antmicro/lpddr5-testbed/assets/previews/layer2.png

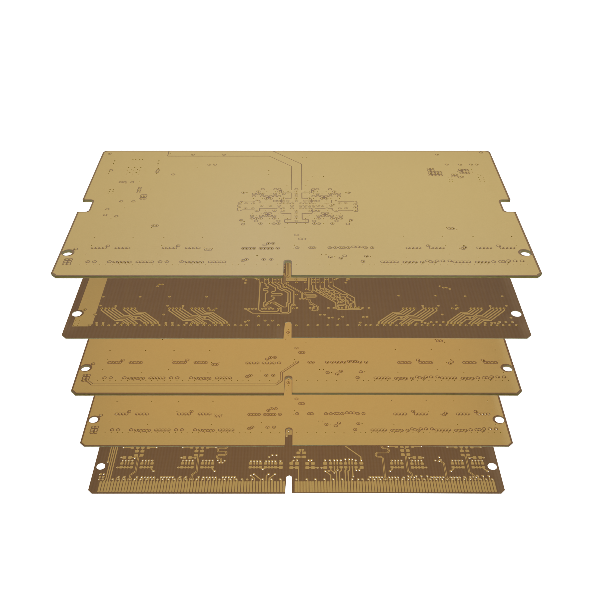
assets/previews/layer2.png
