antmicro/lpddr5-testbed/assets/previews/layer3.webp

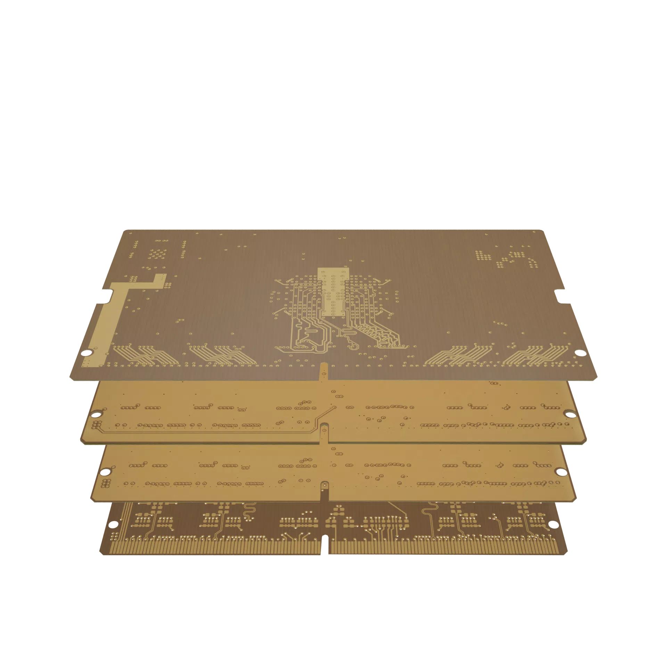
assets/previews/layer3.webp
