antmicro/lpddr5-testbed/assets/previews/layer4.png

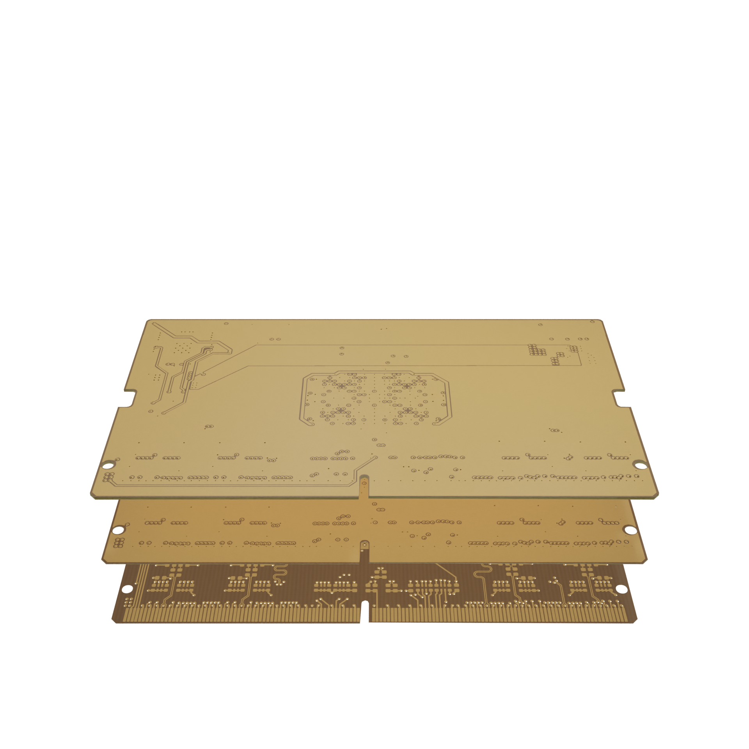
assets/previews/layer4.png
