antmicro/lpddr5-testbed/assets/previews/layer5.png

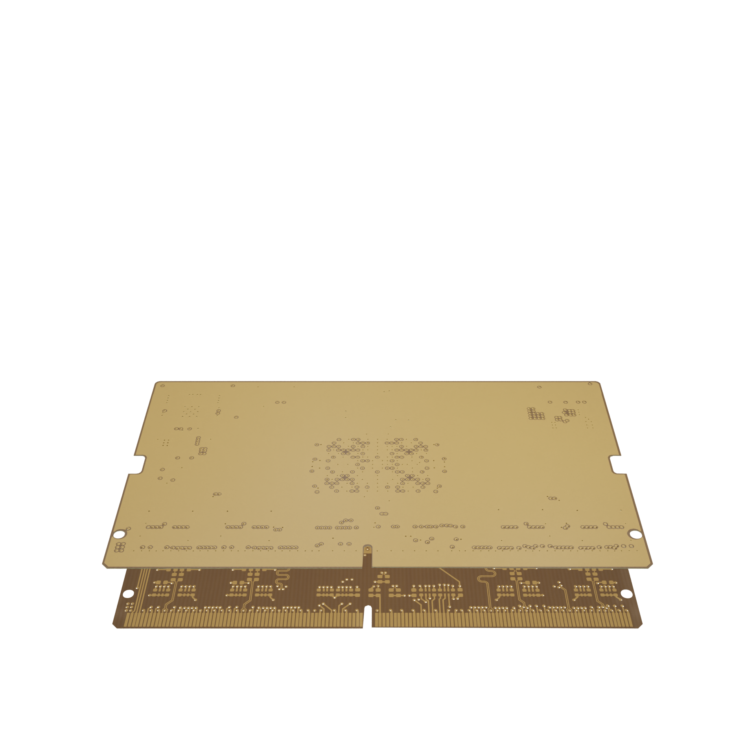
assets/previews/layer5.png
