antmicro/lpddr5-testbed/assets/previews/leftB.png

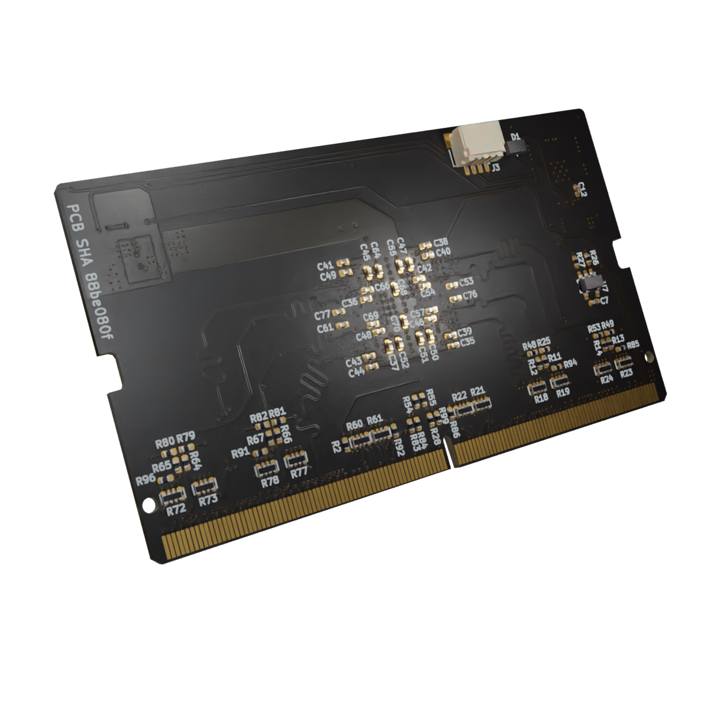
assets/previews/leftB.png
