antmicro/lpddr5-testbed/assets/previews/orthoB.png

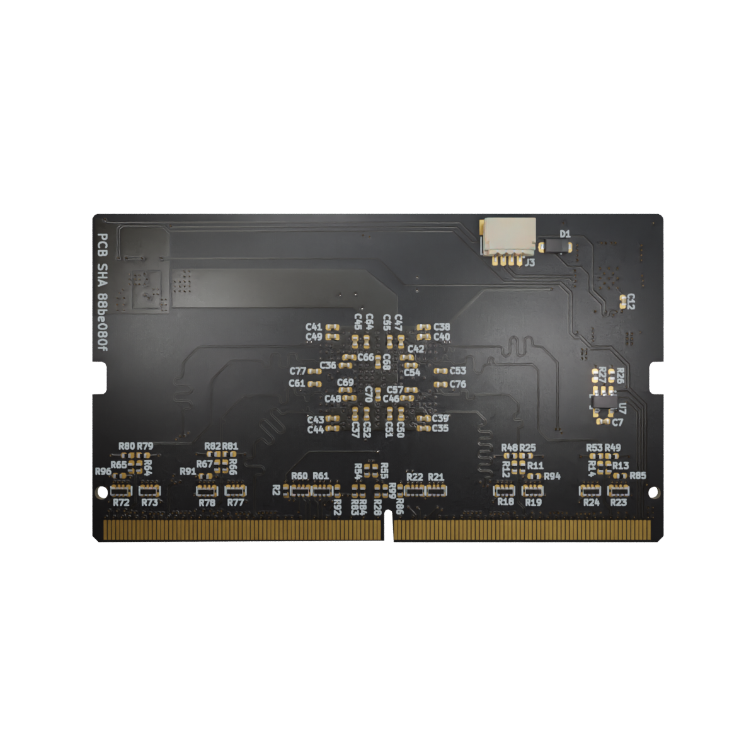
assets/previews/orthoB.png
