antmicro/lpddr5-testbed/assets/previews/orthoT.png

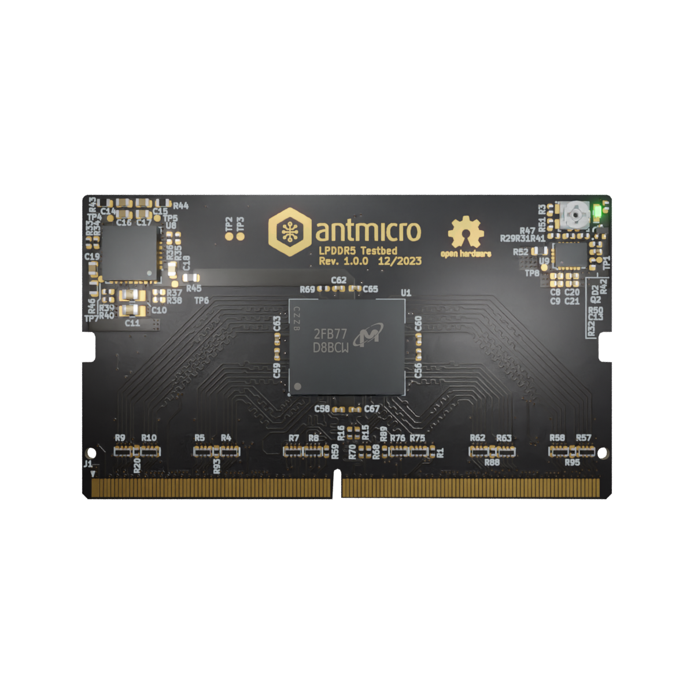
assets/previews/orthoT.png
