antmicro/lpddr5-testbed/assets/previews/photoB.png

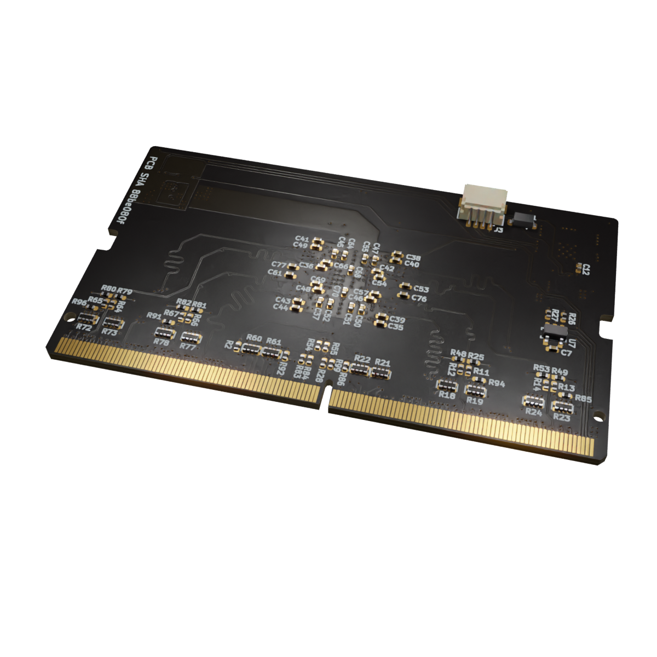
assets/previews/photoB.png
