antmicro/lpddr5-testbed/assets/previews/rightB.png

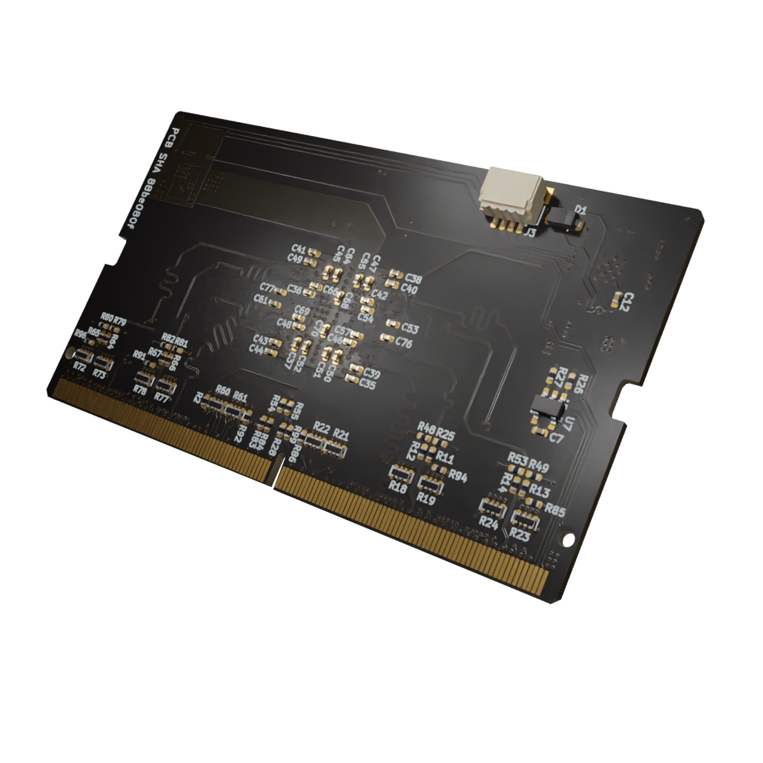
assets/previews/rightB.png
