antmicro/lpddr5-testbed/lpddr5-testbed.kicad_sch

## KiCad design lpddr5-testbed.kicad_sch (2024-01-10)

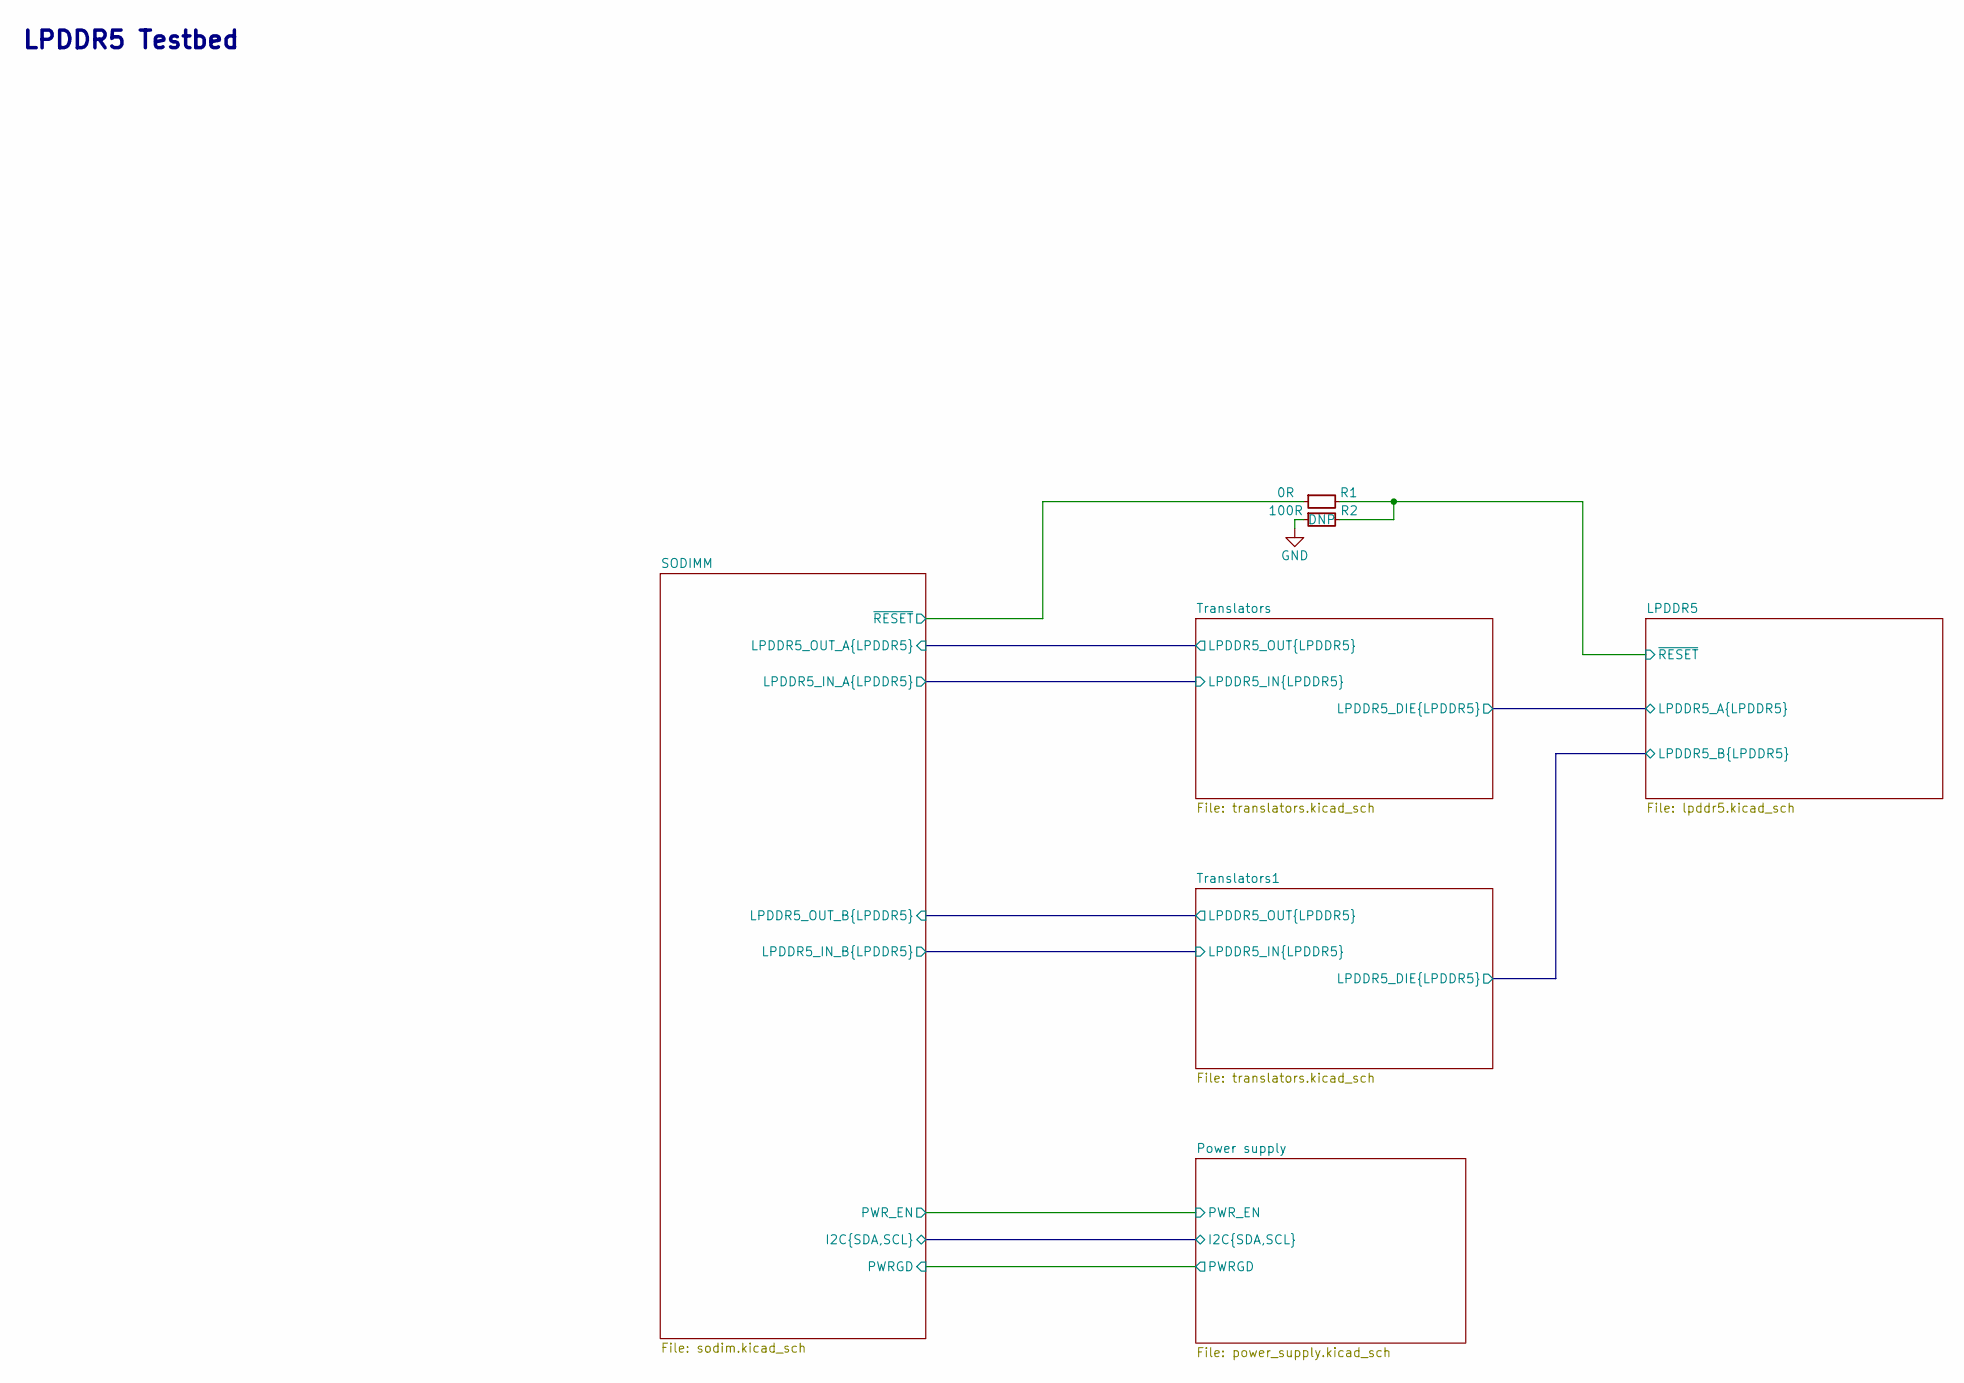
[picture p19: schematic lpddr5-testbed.kicad_sch]

Parts:
R1: R_0R_0402; R_0402_1005Metric; MPN ERJ2GE0R00X
R2: R_100R_0402; R_0402_1005Metric; Tolerance 1%; MPN CR0402-FX-1000GLF

Connections:
GND: R2.1
~RESET: R1.1, R1.2, R2.2

Notes on the sheet:
LPDDR5 Testbed
