antmicro/lpddr5-testbed/lpddr5.kicad_sch

## KiCad design lpddr5.kicad_sch (2023-12-29)

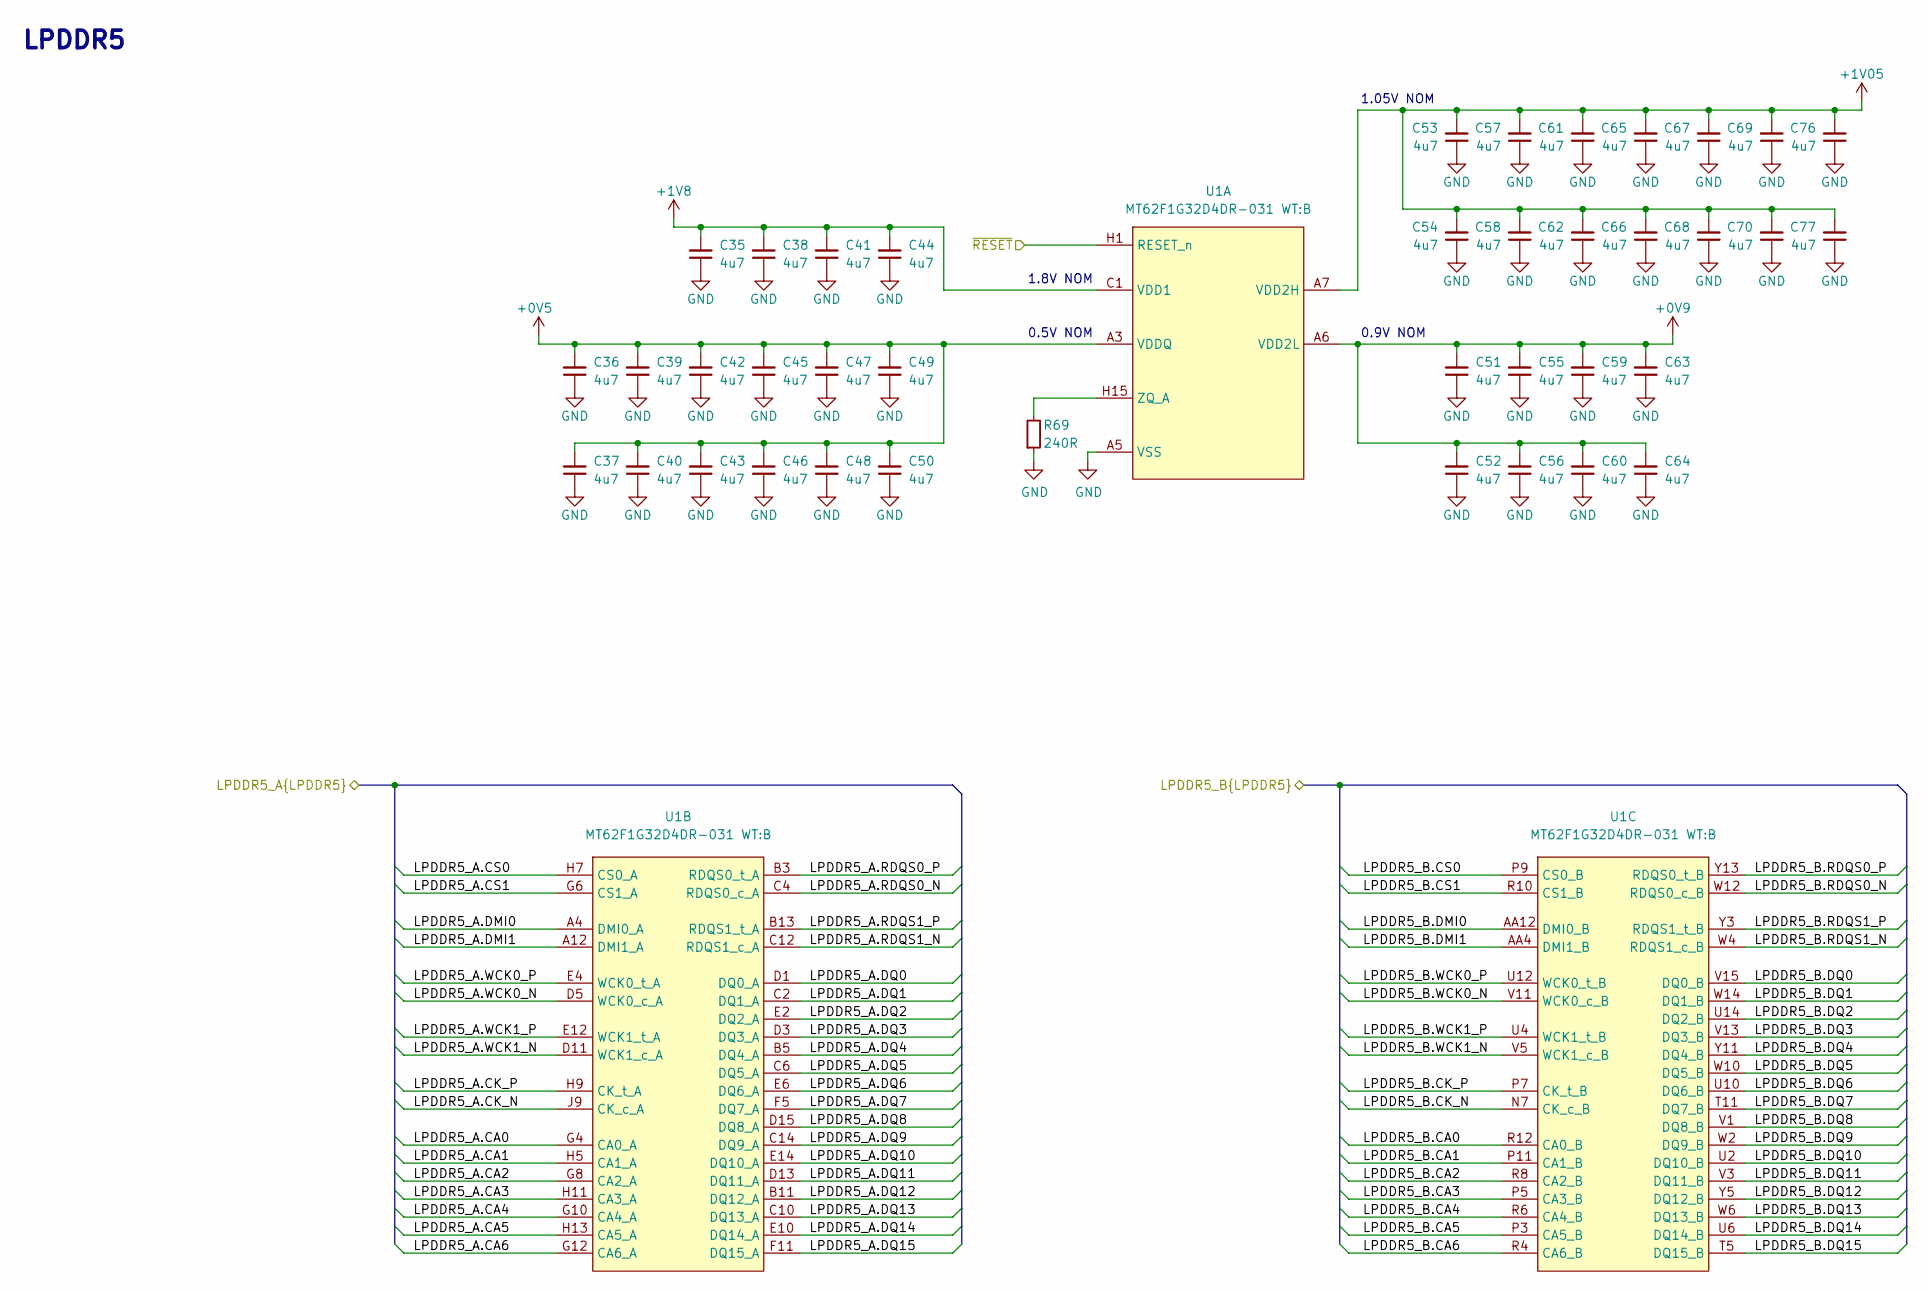
[picture p20: schematic lpddr5.kicad_sch]

Parts:
C35, C36, C37, C38, C39, C40, C41, C42, C43, C44, C45, C46, C47, C48, C49, C50, C51, C52, C53, C54, C55, C56, C57, C58, C59, C60, C61, C62, C63, C64, C65, C66, C67, C68, C69, C70, C76, C77: C_4u7_0402; C_0402_1005Metric; MPN GRM155R61A475MEAAD
R69: R_240R_0402; R_0402_1005Metric; Tolerance 1%; MPN CR0402-FX-2400GLF
U1: MT62F1G32D4DR-031; BGA-315_12.4x15mm_Layout15x21_P0.8x0.7mm; MPN MT62F1G32D4DR-031 WT:B

Connections:
+0V5: C36.2, C37.2, C39.2, C40.2, C42.2, C43.2, C45.2, C46.2, C47.2, C48.2, C49.2, C50.2, U1.A3 (VDDQ), U1.A13 (VDDQ), U1.AA3 (VDDQ), U1.AA13 (VDDQ), U1.B2 (VDDQ), U1.B14 (VDDQ), U1.C3 (VDDQ), U1.C13 (VDDQ), U1.D4 (VDDQ), U1.D12 (VDDQ), U1.E5 (VDDQ), U1.E11 (VDDQ), U1.F1 (VDDQ), U1.F3 (VDDQ), U1.F4 (VDDQ), U1.F12 (VDDQ), U1.F13 (VDDQ), U1.F15 (VDDQ), U1.G1 (VDDQ), U1.G2 (VDDQ), U1.G14 (VDDQ), U1.G15 (VDDQ), U1.R1 (VDDQ), U1.R2 (VDDQ), U1.R14 (VDDQ), U1.R15 (VDDQ), U1.T1 (VDDQ), U1.T3 (VDDQ), U1.T4 (VDDQ), U1.T12 (VDDQ), U1.T13 (VDDQ), U1.T15 (VDDQ), U1.U5 (VDDQ), U1.U11 (VDDQ), U1.V4 (VDDQ), U1.V12 (VDDQ), U1.W3 (VDDQ), U1.W13 (VDDQ), U1.Y2 (VDDQ), U1.Y14 (VDDQ)
+0V9: C51.2, C52.2, C55.2, C56.2, C59.2, C60.2, C63.2, C64.2, U1.A6 (VDD2L), U1.A10 (VDD2L), U1.AA6 (VDD2L), U1.AA10 (VDD2L), U1.B6 (VDD2L), U1.B10 (VDD2L), U1.H2 (VDD2L), U1.H14 (VDD2L), U1.J2 (VDD2L), U1.J14 (VDD2L), U1.N2 (VDD2L), U1.N14 (VDD2L), U1.P2 (VDD2L), U1.P14 (VDD2L), U1.Y6 (VDD2L), U1.Y10 (VDD2L)
+1V05: C53.2, C54.2, C57.2, C58.2, C61.2, C62.2, C65.2, C66.2, C67.2, C68.2, C69.2, C70.2, C76.2, C77.2, U1.A7 (VDD2H), U1.A8 (VDD2H), U1.A9 (VDD2H), U1.AA7 (VDD2H), U1.AA8 (VDD2H), U1.AA9 (VDD2H), U1.B7 (VDD2H), U1.B9 (VDD2H), U1.C7 (VDD2H), U1.C9 (VDD2H), U1.D8 (VDD2H), U1.E7 (VDD2H), U1.E9 (VDD2H), U1.F6 (VDD2H), U1.F7 (VDD2H), U1.F9 (VDD2H), U1.F10 (VDD2H), U1.J5 (VDD2H), U1.J11 (VDD2H), U1.K1 (VDD2H), U1.K2 (VDD2H), U1.K3 (VDD2H), U1.K4 (VDD2H), U1.K5 (VDD2H), U1.K6 (VDD2H), U1.K10 (VDD2H), U1.K11 (VDD2H), U1.K12 (VDD2H), U1.K13 (VDD2H), U1.K14 (VDD2H), U1.K15 (VDD2H), U1.L6 (VDD2H), U1.L7 (VDD2H), U1.L8 (VDD2H), U1.L9 (VDD2H), U1.L10 (VDD2H), U1.M1 (VDD2H), U1.M2 (VDD2H), U1.M3 (VDD2H), U1.M4 (VDD2H), U1.M5 (VDD2H), U1.M6 (VDD2H), U1.M10 (VDD2H), U1.M11 (VDD2H), U1.M12 (VDD2H), U1.M13 (VDD2H), U1.M14 (VDD2H), U1.M15 (VDD2H), U1.N5 (VDD2H), U1.N11 (VDD2H), U1.T6 (VDD2H), U1.T7 (VDD2H), U1.T9 (VDD2H), U1.T10 (VDD2H), U1.U7 (VDD2H), U1.U9 (VDD2H), U1.V8 (VDD2H), U1.W7 (VDD2H), U1.W9 (VDD2H), U1.Y7 (VDD2H), U1.Y9 (VDD2H)
+1V8: C35.2, C38.2, C41.2, C44.2, U1.C1 (VDD1), U1.C15 (VDD1), U1.W1 (VDD1), U1.W15 (VDD1)
GND: C35.1, C36.1, C37.1, C38.1, C39.1, C40.1, C41.1, C42.1, C43.1, C44.1, C45.1, C46.1, C47.1, C48.1, C49.1, C50.1, C51.1, C52.1, C53.1, C54.1, C55.1, C56.1, C57.1, C58.1, C59.1, C60.1, C61.1, C62.1, C63.1, C64.1, C65.1, C66.1, C67.1, C68.1, C69.1, C70.1, C76.1, C77.1, R69.1, U1.A5 (VSS), U1.A11 (VSS), U1.AA5 (VSS), U1.AA11 (VSS), U1.B4 (VSS), U1.B8 (VSS), U1.B12 (VSS), U1.C5 (VSS), U1.C8 (VSS), U1.C11 (VSS), U1.D2 (VSS), U1.D6 (VSS), U1.D7 (VSS), U1.D9 (VSS), U1.D10 (VSS), U1.D14 (VSS), U1.E1 (VSS), U1.E3 (VSS), U1.E8 (VSS), U1.E13 (VSS), U1.E15 (VSS), U1.F2 (VSS), U1.F8 (VSS), U1.F14 (VSS), U1.G3 (VSS), U1.G5 (VSS), U1.G7 (VSS), U1.G9 (VSS), U1.G11 (VSS), U1.G13 (VSS), U1.H3 (VSS), U1.H4 (VSS), U1.H6 (VSS), U1.H8 (VSS), U1.H10 (VSS), U1.H12 (VSS), U1.J1 (VSS), U1.J3 (VSS), U1.J7 (VSS), U1.J8 (VSS), U1.J10 (VSS), U1.J12 (VSS), U1.J13 (VSS), U1.J15 (VSS), U1.K7 (VSS), U1.K8 (VSS), U1.K9 (VSS), U1.L1 (VSS), U1.L2 (VSS), U1.L3 (VSS), U1.L4 (VSS), U1.L5 (VSS), U1.L11 (VSS), U1.L12 (VSS), U1.L13 (VSS), U1.L14 (VSS), U1.L15 (VSS), U1.M7 (VSS), U1.M8 (VSS), U1.M9 (VSS), U1.N1 (VSS), U1.N3 (VSS), U1.N4 (VSS), U1.N6 (VSS), U1.N8 (VSS), U1.N9 (VSS), U1.N10 (VSS), U1.N12 (VSS), U1.N13 (VSS), U1.N15 (VSS), U1.P4 (VSS), U1.P6 (VSS), U1.P8 (VSS), U1.P10 (VSS), U1.P12 (VSS), U1.P13 (VSS), U1.R3 (VSS), U1.R5 (VSS), U1.R7 (VSS), U1.R9 (VSS), U1.R11 (VSS), U1.R13 (VSS), U1.T2 (VSS), U1.T8 (VSS), U1.T14 (VSS), U1.U1 (VSS), U1.U3 (VSS), U1.U8 (VSS), U1.U13 (VSS), U1.U15 (VSS), U1.V2 (VSS), U1.V6 (VSS), U1.V7 (VSS), U1.V9 (VSS), U1.V10 (VSS), U1.V14 (VSS), U1.W5 (VSS), U1.W8 (VSS), U1.W11 (VSS), U1.Y4 (VSS), U1.Y8 (VSS), U1.Y12 (VSS)
LPDDR5_A.CA0: U1.G4 (CA0_A)
LPDDR5_A.CA1: U1.H5 (CA1_A)
LPDDR5_A.CA2: U1.G8 (CA2_A)
LPDDR5_A.CA3: U1.H11 (CA3_A)
LPDDR5_A.CA4: U1.G10 (CA4_A)
LPDDR5_A.CA5: U1.H13 (CA5_A)
LPDDR5_A.CA6: U1.G12 (CA6_A)
LPDDR5_A.CK_N: U1.J9 (CK_c_A)
LPDDR5_A.CK_P: U1.H9 (CK_t_A)
LPDDR5_A.CS0: U1.H7 (CS0_A)
LPDDR5_A.CS1: U1.G6 (CS1_A)
LPDDR5_A.DMI0: U1.A4 (DMI0_A)
LPDDR5_A.DMI1: U1.A12 (DMI1_A)
LPDDR5_A.DQ0: U1.D1 (DQ0_A)
LPDDR5_A.DQ1: U1.C2 (DQ1_A)
LPDDR5_A.DQ2: U1.E2 (DQ2_A)
LPDDR5_A.DQ3: U1.D3 (DQ3_A)
LPDDR5_A.DQ4: U1.B5 (DQ4_A)
LPDDR5_A.DQ5: U1.C6 (DQ5_A)
LPDDR5_A.DQ6: U1.E6 (DQ6_A)
LPDDR5_A.DQ7: U1.F5 (DQ7_A)
LPDDR5_A.DQ8: U1.D15 (DQ8_A)
LPDDR5_A.DQ9: U1.C14 (DQ9_A)
LPDDR5_A.DQ10: U1.E14 (DQ10_A)
LPDDR5_A.DQ11: U1.D13 (DQ11_A)
LPDDR5_A.DQ12: U1.B11 (DQ12_A)
LPDDR5_A.DQ13: U1.C10 (DQ13_A)
LPDDR5_A.DQ14: U1.E10 (DQ14_A)
LPDDR5_A.DQ15: U1.F11 (DQ15_A)
LPDDR5_A.RDQS0_N: U1.C4 (RDQS0_c_A)
LPDDR5_A.RDQS0_P: U1.B3 (RDQS0_t_A)
LPDDR5_A.RDQS1_N: U1.C12 (RDQS1_c_A)
LPDDR5_A.RDQS1_P: U1.B13 (RDQS1_t_A)
LPDDR5_A.WCK0_N: U1.D5 (WCK0_c_A)
LPDDR5_A.WCK0_P: U1.E4 (WCK0_t_A)
LPDDR5_A.WCK1_N: U1.D11 (WCK1_c_A)
LPDDR5_A.WCK1_P: U1.E12 (WCK1_t_A)
LPDDR5_B.CA0: U1.R12 (CA0_B)
LPDDR5_B.CA1: U1.P11 (CA1_B)
LPDDR5_B.CA2: U1.R8 (CA2_B)
LPDDR5_B.CA3: U1.P5 (CA3_B)
LPDDR5_B.CA4: U1.R6 (CA4_B)
LPDDR5_B.CA5: U1.P3 (CA5_B)
LPDDR5_B.CA6: U1.R4 (CA6_B)
LPDDR5_B.CK_N: U1.N7 (CK_c_B)
LPDDR5_B.CK_P: U1.P7 (CK_t_B)
LPDDR5_B.CS0: U1.P9 (CS0_B)
LPDDR5_B.CS1: U1.R10 (CS1_B)
LPDDR5_B.DMI0: U1.AA12 (DMI0_B)
LPDDR5_B.DMI1: U1.AA4 (DMI1_B)
LPDDR5_B.DQ0: U1.V15 (DQ0_B)
LPDDR5_B.DQ1: U1.W14 (DQ1_B)
LPDDR5_B.DQ2: U1.U14 (DQ2_B)
LPDDR5_B.DQ3: U1.V13 (DQ3_B)
LPDDR5_B.DQ4: U1.Y11 (DQ4_B)
LPDDR5_B.DQ5: U1.W10 (DQ5_B)
LPDDR5_B.DQ6: U1.U10 (DQ6_B)
LPDDR5_B.DQ7: U1.T11 (DQ7_B)
LPDDR5_B.DQ8: U1.V1 (DQ8_B)
LPDDR5_B.DQ9: U1.W2 (DQ9_B)
LPDDR5_B.DQ10: U1.U2 (DQ10_B)
LPDDR5_B.DQ11: U1.V3 (DQ11_B)
LPDDR5_B.DQ12: U1.Y5 (DQ12_B)
LPDDR5_B.DQ13: U1.W6 (DQ13_B)
LPDDR5_B.DQ14: U1.U6 (DQ14_B)
LPDDR5_B.DQ15: U1.T5 (DQ15_B)
LPDDR5_B.RDQS0_N: U1.W12 (RDQS0_c_B)
LPDDR5_B.RDQS0_P: U1.Y13 (RDQS0_t_B)
LPDDR5_B.RDQS1_N: U1.W4 (RDQS1_c_B)
LPDDR5_B.RDQS1_P: U1.Y3 (RDQS1_t_B)
LPDDR5_B.WCK0_N: U1.V11 (WCK0_c_B)
LPDDR5_B.WCK0_P: U1.U12 (WCK0_t_B)
LPDDR5_B.WCK1_N: U1.V5 (WCK1_c_B)
LPDDR5_B.WCK1_P: U1.U4 (WCK1_t_B)
unnamed: R69.2, U1.H15 (ZQ_A)
~RESET: U1.H1 (RESET_n)

Notes on the sheet:
0.5V NOM
0.9V NOM
1.05V NOM
LPDDR5
1.8V NOM
