antmicro/lpddr5-testbed/power_supply.kicad_sch

## KiCad design power_supply.kicad_sch (2024-01-03)

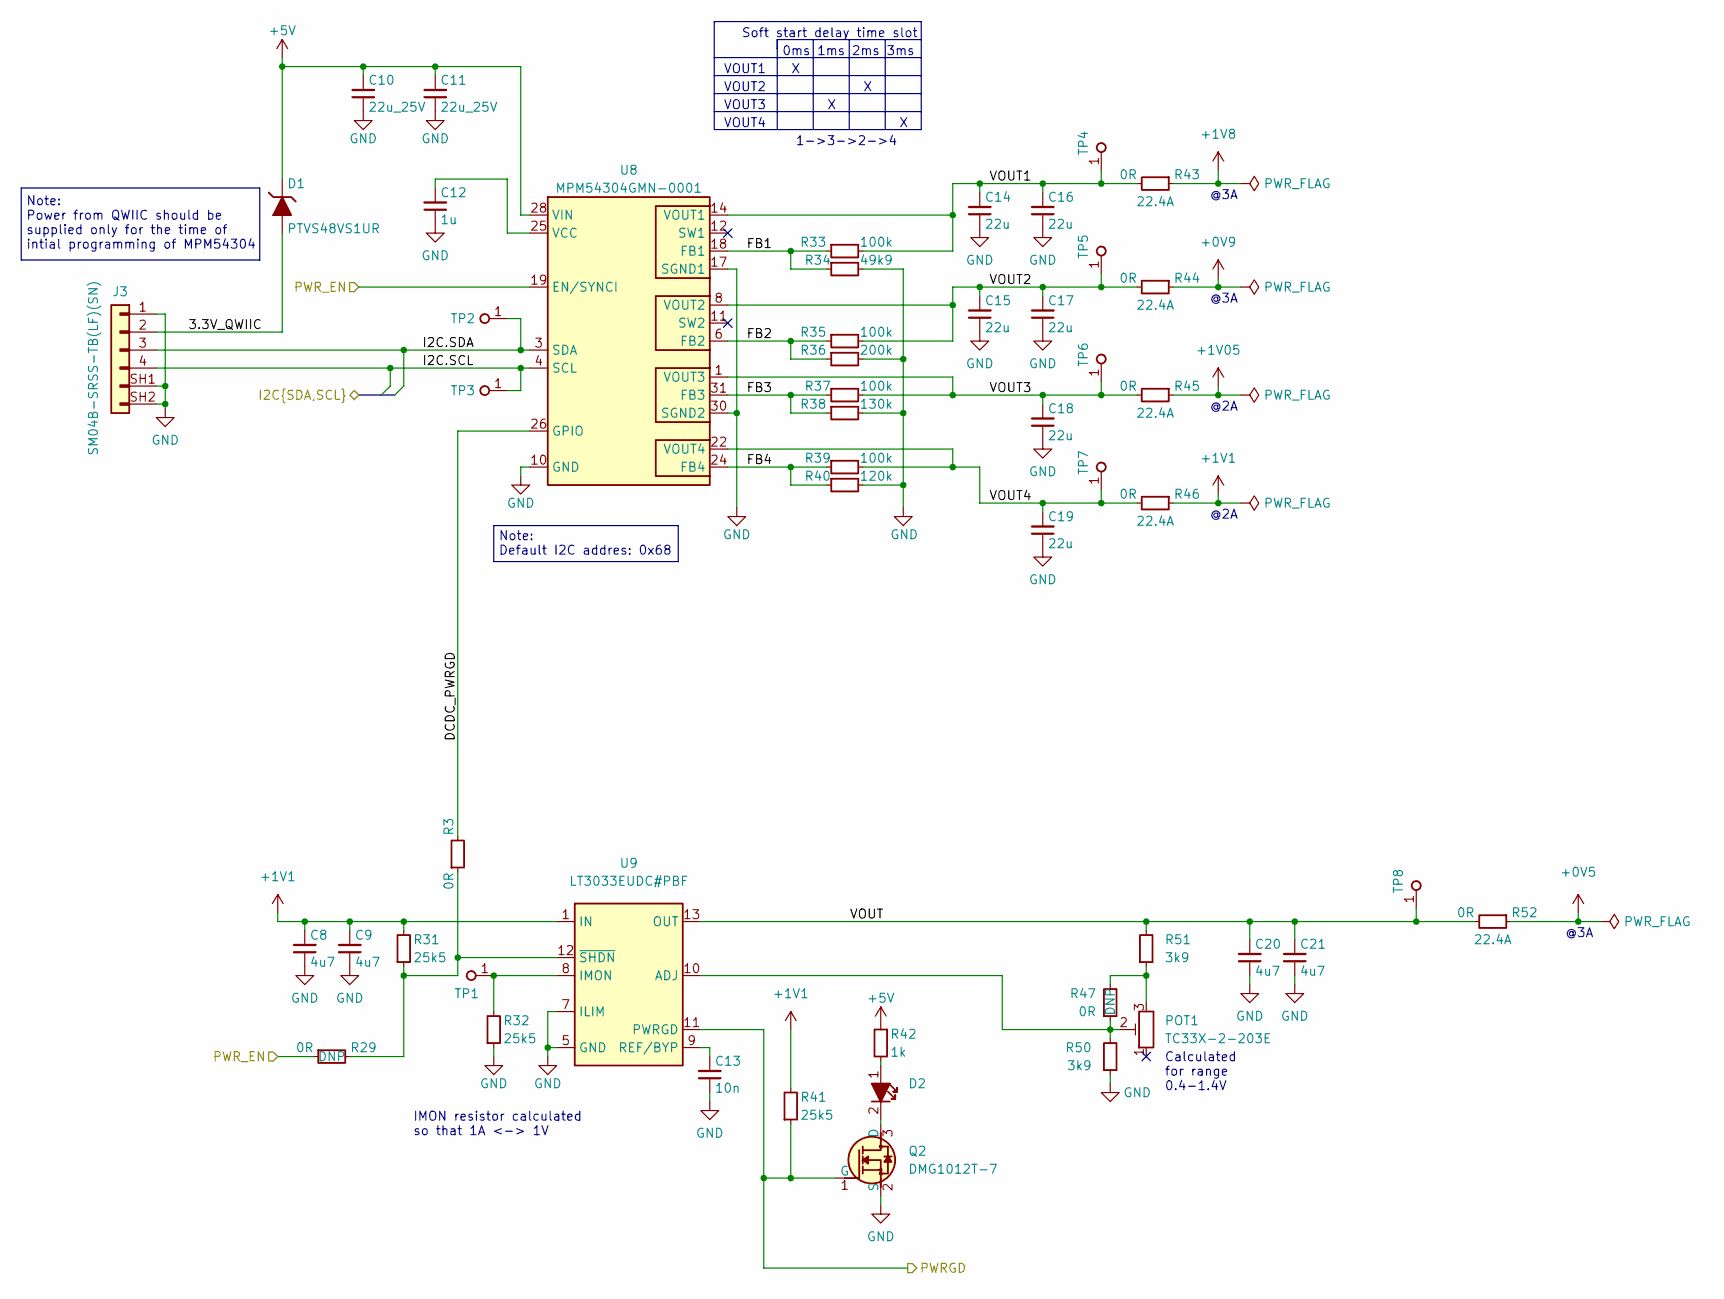
[picture p21: schematic power_supply.kicad_sch]

Parts:
C8, C9, C20, C21: C_4u7_0402; C_0402_1005Metric; MPN GRM155R61A475MEAAD
C10, C11: C_22u_25V_0805; C_0805_2012Metric; MPN CL21A226MAYNNNE
C12: C_1u_0402; C_0402_1005Metric; MPN C1005X6S1A105K050BC
C13: C_10n_0402; C_0402_1005Metric; Voltage 50V; MPN GRM155R71H103KA88D
C14, C15, C16, C17, C18, C19: C_22u_0603; C_0603_1608Metric; MPN GRM188R60J226MEA0D
D1: PTVS48VS1UR; D_SOD-123F; MPN PTVS48VS1UR,115
D2: LED_G_0603_KP-1608CGCK; LED_0603_1608Metric_G; MPN KP-1608CGCK
J3: JST_SH_1x4_SM04B-SRSS-TB-LF-SN; Conn_JST_SH_1x4_SM04B-SRSS-TB-LF-SN; MPN SM04B-SRSS-TB(LF)(SN)
POT1: TC33X-2-203E; Trimpot_3.8mmx3.6mm_TC33X-2-103E; MPN TC33X-2-203E
Q2: DMG1012T-7; SOT-523; MPN DMG1012T-7
R3, R29, R47: R_0R_0402; R_0402_1005Metric; MPN ERJ2GE0R00X
R31, R32, R41: R_25k5_0402; R_0402_1005Metric; Tolerance 1%; MPN CR0402-FX-2552GLF
R33, R35, R37, R39: R_100k_0402; R_0402_1005Metric; Tolerance 1%; MPN CR0402-FX-1003GLF
R34: R_49k9_0402; R_0402_1005Metric; Tolerance 1%; MPN CR0402-FX-4992GLF
R36: R_200k_0402; R_0402_1005Metric; Tolerance 1%; MPN CR0402-FX-2003GLF
R38: R_130k_0402; R_0402_1005Metric; Tolerance 1%; MPN CR0402-FX-1303GLF
R40: R_120k_0402; R_0402_1005Metric; Tolerance 1%; MPN CR0402-FX-1203GLF
R42: R_1k_0402; R_0402_1005Metric; Tolerance 1%; MPN CR0402-FX-1001GLF
R43, R44, R45, R46, R52: R_0R_22.4A_0603; R_0603_1608Metric; Tolerance template_tolerance; MPN PMR03EZPJ000
R50, R51: R_3k9_0402; R_0402_1005Metric; Tolerance 1%; MPN CR0402-FX-3901GLF
TP1, TP4, TP5, TP6, TP7, TP8: TP_0.75mm_SMD; TP_SMD_0.75mm
TP2, TP3: TP_1mm_SMD; TP_SMD_1mm
U8: MPM54304GMN-0001; LGA-33_7x7mm_P0.65mm; MPN MPM54304GMN-0001
U9: LT3033EUDC_QFN; QFN-20-4EP_3x4x0.75mm_P0.5mm_Layout4x6_LT3033; MPN LT3033EUDC#PBF

Connections:
3.3V_QWIIC: D1.A, J3.2
+0V5: R52.1
+0V9: R44.1
+1V1: C8.2, C9.2, R31.2, R41.2, R46.1, U9.1 (IN), U9.2 (IN), U9.15 (IN), U9.16 (IN), U9.21 (IN), U9.22 (IN)
+1V05: R45.1
+1V8: R43.1
+5V: C10.2, C11.2, D1.K (C), R42.1, U8.28 (VIN), U8.29 (VIN)
DCDC_PWRGD: R3.2, U8.26 (GPIO)
FB1: R33.1, R34.1, U8.18 (FB1)
FB2: R35.1, R36.1, U8.6 (FB2)
FB3: R37.1, R38.1, U8.31 (FB3)
FB4: R39.1, R40.1, U8.24 (FB4)
GND: C8.1, C9.1, C10.1, C11.1, C12.1, C13.1, C14.1, C15.1, C16.1, C17.1, C18.1, C19.1, C20.1, C21.1, J3.1, J3.SH1, J3.SH2, Q2.2 (S), R32.1, R34.2, R36.2, R38.2, R40.2, R50.1, U8.2 (GND), U8.5 (GND), U8.7 (GND), U8.10 (GND), U8.13 (GND), U8.16 (GND), U8.17 (SGND1), U8.20 (GND), U8.21 (GND), U8.27 (GND), U8.30 (SGND2), U8.33 (GND), U9.5 (GND), U9.6 (GND), U9.7 (ILIM)
I2C.SCL: J3.4, TP3.1, U8.4 (SCL)
I2C.SDA: J3.3, TP2.1, U8.3 (SDA)
unnamed: C12.2, U8.25 (VCC)
unnamed: C13.2, U9.9 (REF/BYP)
unnamed: D2.1, R42.2
unnamed: D2.2, Q2.3 (D)
unnamed: POT1.2, R47.1, R50.2, U9.10 (ADJ)
unnamed: POT1.3, R47.2, R51.1
unnamed: R3.1, R29.2, R31.1, U9.12 (~SHDN)
unnamed: R32.2, TP1.1, U9.8 (IMON)
PWRGD: Q2.1 (G), R41.1, U9.11 (PWRGD)
PWR_EN: R29.1, U8.19 (EN/SYNCI)
VOUT: C20.2, C21.2, R51.2, R52.2, TP8.1, U9.3 (OUT), U9.4 (OUT), U9.13 (OUT), U9.14 (OUT), U9.17 (OUT), U9.18 (OUT), U9.19 (OUT), U9.20 (OUT), U9.23 (OUT), U9.24 (OUT)
VOUT1: C14.2, C16.2, R33.2, R43.2, TP4.1, U8.14 (VOUT1), U8.15 (VOUT1)
VOUT2: C15.2, C17.2, R35.2, R44.2, TP5.1, U8.8 (VOUT2), U8.9 (VOUT2)
VOUT3: C18.2, R37.2, R45.2, TP6.1, U8.1 (VOUT3), U8.32 (VOUT3)
VOUT4: C19.2, R39.2, R46.2, TP7.1, U8.22 (VOUT4), U8.23 (VOUT4)

Notes on the sheet:
@2A
Soft start delay time slot
VOUT4
VOUT1
@3A
Note: Default I2C addres: 0x68
Note: Power from QWIIC should be supplied only for the time of intial programming of MPM54304
Calculated for range 0.4-1.4V
1->3->2->4
VOUT3
VOUT2
0ms 1ms 2ms 3ms
IMON resistor calculated so that 1A <-> 1V
