antmicro/lpddr5-testbed/sodim.kicad_sch

## KiCad design sodim.kicad_sch (2024-01-03)

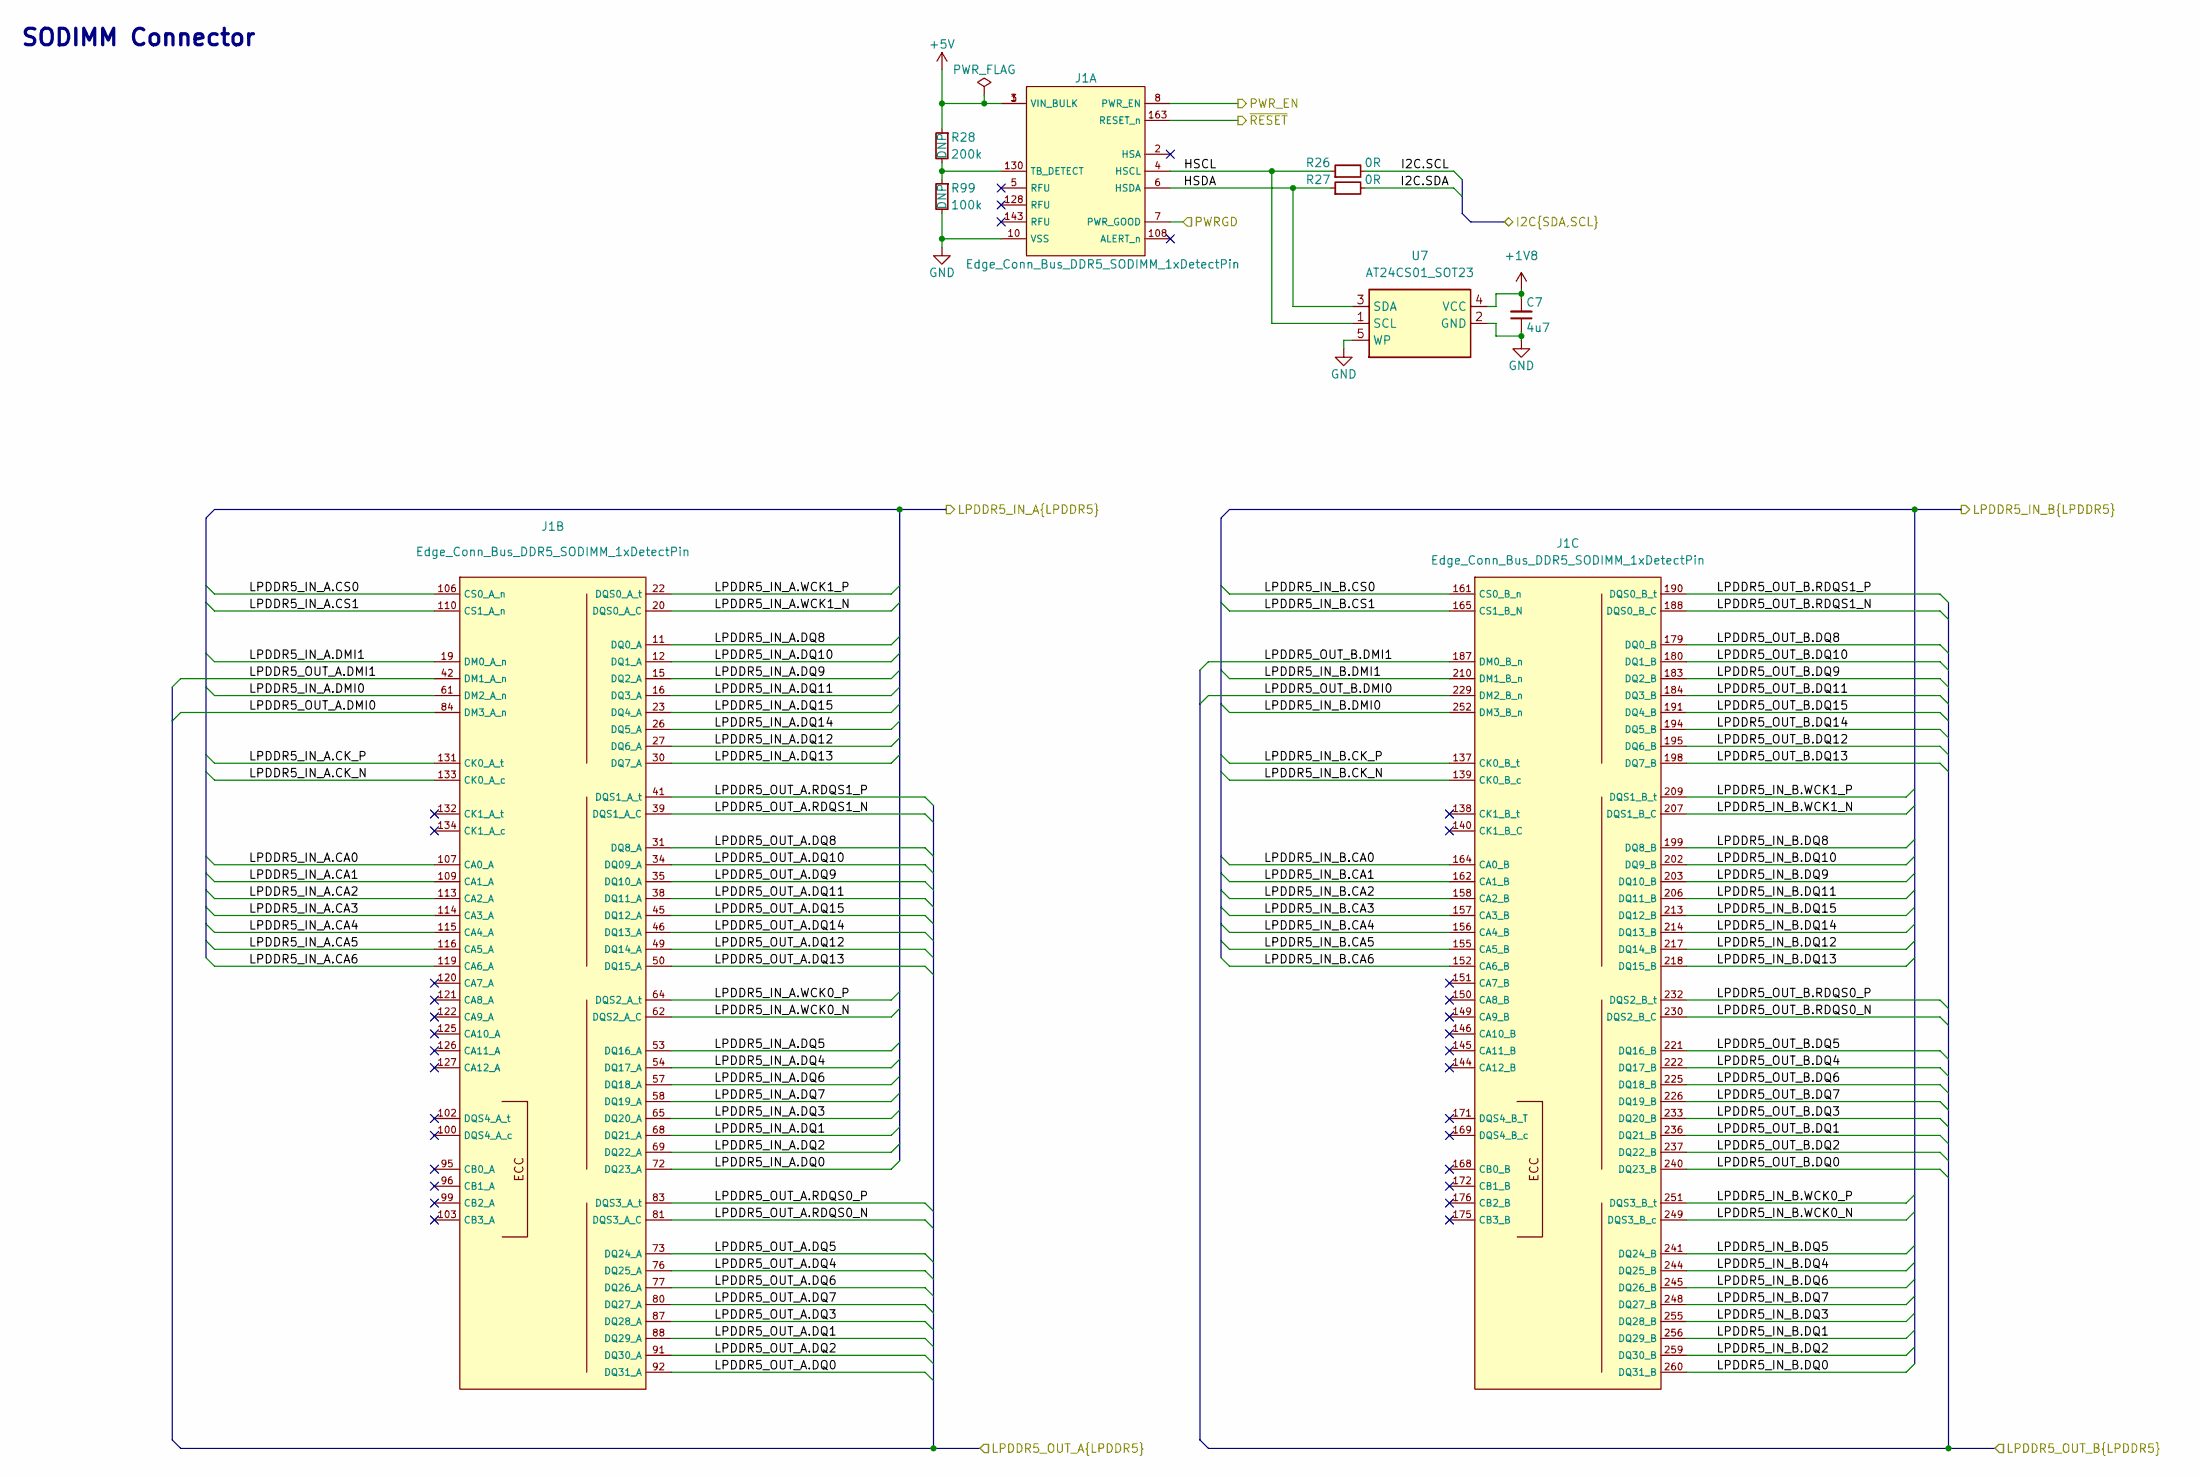
[picture p22: schematic sodim.kicad_sch]

Parts:
C7: C_4u7_0402; C_0402_1005Metric; MPN GRM155R61A475MEAAD
J1: Edge_Conn_Bus_DDR5_SODIMM_1xDetectPin; Edge_Conn_Bus_DDR5_SODIMM
R26, R27: R_0R_0402; R_0402_1005Metric; MPN ERJ2GE0R00X
R28: R_200k_0402; R_0402_1005Metric; Tolerance 1%; MPN CR0402-FX-2003GLF
R99: R_100k_0402; R_0402_1005Metric; Tolerance 1%; MPN CR0402-FX-1003GLF
U7: AT24CS01_SOT23; SOT-23-5; MPN AT24CS01-ST

Connections:
+1V8: C7.2, U7.4 (VCC)
+5V: J1.1 (VIN_BULK), J1.3 (VIN_BULK), R28.1
GND: C7.1, J1.9 (VSS), J1.10 (VSS), J1.13 (VSS), J1.14 (VSS), J1.17 (VSS), J1.18 (VSS), J1.21 (VSS), J1.24 (VSS), J1.25 (VSS), J1.28 (VSS), J1.29 (VSS), J1.32 (VSS), J1.33 (VSS), J1.36 (VSS), J1.37 (VSS), J1.40 (VSS), J1.43 (VSS), J1.44 (VSS), J1.47 (VSS), J1.48 (VSS), J1.51 (VSS), J1.52 (VSS), J1.55 (VSS), J1.56 (VSS), J1.59 (VSS), J1.60 (VSS), J1.63 (VSS), J1.66 (VSS), J1.67 (VSS), J1.70 (VSS), J1.71 (VSS), J1.74 (VSS), J1.75 (VSS), J1.78 (VSS), J1.79 (VSS), J1.82 (VSS), J1.85 (VSS), J1.86 (VSS), J1.89 (VSS), J1.90 (VSS), J1.93 (VSS), J1.94 (VSS), J1.97 (VSS), J1.98 (VSS), J1.101 (VSS), J1.104 (VSS), J1.105 (VSS), J1.111 (VSS), J1.112 (VSS), J1.117 (VSS), J1.118 (VSS), J1.123 (VSS), J1.124 (VSS), J1.129 (VSS), J1.135 (VSS), J1.136 (VSS), J1.141 (VSS), J1.142 (VSS), J1.147 (VSS), J1.148 (VSS), J1.153 (VSS), J1.154 (VSS), J1.159 (VSS), J1.160 (VSS), J1.166 (VSS), J1.167 (VSS), J1.170 (VSS), J1.173 (VSS), J1.174 (VSS), J1.177 (VSS), J1.178 (VSS), J1.181 (VSS), J1.182 (VSS), J1.185 (VSS), J1.186 (VSS), J1.189 (VSS), J1.192 (VSS), J1.193 (VSS), J1.196 (VSS), J1.197 (VSS), J1.200 (VSS), J1.201 (VSS), J1.204 (VSS), J1.205 (VSS), J1.208 (VSS), J1.211 (VSS), J1.212 (VSS), J1.215 (VSS), J1.216 (VSS), J1.219 (VSS), J1.220 (VSS), J1.223 (VSS), J1.224 (VSS), J1.227 (VSS), J1.228 (VSS), J1.231 (VSS), J1.234 (VSS), J1.235 (VSS), J1.238 (VSS), J1.239 (VSS), J1.242 (VSS), J1.243 (VSS), J1.246 (VSS), J1.247 (VSS), J1.250 (VSS), J1.253 (VSS), J1.254 (VSS), J1.257 (VSS), J1.258 (VSS), J1.261 (VSS), J1.262 (VSS), R99.2, U7.2 (GND), U7.5 (WP)
HSCL: J1.4 (HSCL), R26.1, U7.1 (SCL)
HSDA: J1.6 (HSDA), R27.1, U7.3 (SDA)
I2C.SCL: R26.2
I2C.SDA: R27.2
LPDDR5_IN_A.CA0: J1.107 (CA0_A)
LPDDR5_IN_A.CA1: J1.109 (CA1_A)
LPDDR5_IN_A.CA2: J1.113 (CA2_A)
LPDDR5_IN_A.CA3: J1.114 (CA3_A)
LPDDR5_IN_A.CA4: J1.115 (CA4_A)
LPDDR5_IN_A.CA5: J1.116 (CA5_A)
LPDDR5_IN_A.CA6: J1.119 (CA6_A)
LPDDR5_IN_A.CK_N: J1.133 (CK0_A_c)
LPDDR5_IN_A.CK_P: J1.131 (CK0_A_t)
LPDDR5_IN_A.CS0: J1.106 (CS0_A_n)
LPDDR5_IN_A.CS1: J1.110 (CS1_A_n)
LPDDR5_IN_A.DMI0: J1.61 (DM2_A_n)
LPDDR5_IN_A.DMI1: J1.19 (DM0_A_n)
LPDDR5_IN_A.DQ0: J1.72 (DQ23_A)
LPDDR5_IN_A.DQ1: J1.68 (DQ21_A)
LPDDR5_IN_A.DQ2: J1.69 (DQ22_A)
LPDDR5_IN_A.DQ3: J1.65 (DQ20_A)
LPDDR5_IN_A.DQ4: J1.54 (DQ17_A)
LPDDR5_IN_A.DQ5: J1.53 (DQ16_A)
LPDDR5_IN_A.DQ6: J1.57 (DQ18_A)
LPDDR5_IN_A.DQ7: J1.58 (DQ19_A)
LPDDR5_IN_A.DQ8: J1.11 (DQ0_A)
LPDDR5_IN_A.DQ9: J1.15 (DQ2_A)
LPDDR5_IN_A.DQ10: J1.12 (DQ1_A)
LPDDR5_IN_A.DQ11: J1.16 (DQ3_A)
LPDDR5_IN_A.DQ12: J1.27 (DQ6_A)
LPDDR5_IN_A.DQ13: J1.30 (DQ7_A)
LPDDR5_IN_A.DQ14: J1.26 (DQ5_A)
LPDDR5_IN_A.DQ15: J1.23 (DQ4_A)
LPDDR5_IN_A.WCK0_N: J1.62 (DQS2_A_C)
LPDDR5_IN_A.WCK0_P: J1.64 (DQS2_A_t)
LPDDR5_IN_A.WCK1_N: J1.20 (DQS0_A_C)
LPDDR5_IN_A.WCK1_P: J1.22 (DQS0_A_t)
LPDDR5_IN_B.CA0: J1.164 (CA0_B)
LPDDR5_IN_B.CA1: J1.162 (CA1_B)
LPDDR5_IN_B.CA2: J1.158 (CA2_B)
LPDDR5_IN_B.CA3: J1.157 (CA3_B)
LPDDR5_IN_B.CA4: J1.156 (CA4_B)
LPDDR5_IN_B.CA5: J1.155 (CA5_B)
LPDDR5_IN_B.CA6: J1.152 (CA6_B)
LPDDR5_IN_B.CK_N: J1.139 (CK0_B_c)
LPDDR5_IN_B.CK_P: J1.137 (CK0_B_t)
LPDDR5_IN_B.CS0: J1.161 (CS0_B_n)
LPDDR5_IN_B.CS1: J1.165 (CS1_B_N)
LPDDR5_IN_B.DMI0: J1.252 (DM3_B_n)
LPDDR5_IN_B.DMI1: J1.210 (DM1_B_n)
LPDDR5_IN_B.DQ0: J1.260 (DQ31_B)
LPDDR5_IN_B.DQ1: J1.256 (DQ29_B)
LPDDR5_IN_B.DQ2: J1.259 (DQ30_B)
LPDDR5_IN_B.DQ3: J1.255 (DQ28_B)
LPDDR5_IN_B.DQ4: J1.244 (DQ25_B)
LPDDR5_IN_B.DQ5: J1.241 (DQ24_B)
LPDDR5_IN_B.DQ6: J1.245 (DQ26_B)
LPDDR5_IN_B.DQ7: J1.248 (DQ27_B)
LPDDR5_IN_B.DQ8: J1.199 (DQ8_B)
LPDDR5_IN_B.DQ9: J1.203 (DQ10_B)
LPDDR5_IN_B.DQ10: J1.202 (DQ9_B)
LPDDR5_IN_B.DQ11: J1.206 (DQ11_B)
LPDDR5_IN_B.DQ12: J1.217 (DQ14_B)
LPDDR5_IN_B.DQ13: J1.218 (DQ15_B)
LPDDR5_IN_B.DQ14: J1.214 (DQ13_B)
LPDDR5_IN_B.DQ15: J1.213 (DQ12_B)
LPDDR5_IN_B.WCK0_N: J1.249 (DQS3_B_c)
LPDDR5_IN_B.WCK0_P: J1.251 (DQS3_B_t)
LPDDR5_IN_B.WCK1_N: J1.207 (DQS1_B_C)
LPDDR5_IN_B.WCK1_P: J1.209 (DQS1_B_t)
LPDDR5_OUT_A.DMI0: J1.84 (DM3_A_n)
LPDDR5_OUT_A.DMI1: J1.42 (DM1_A_n)
LPDDR5_OUT_A.DQ0: J1.92 (DQ31_A)
LPDDR5_OUT_A.DQ1: J1.88 (DQ29_A)
LPDDR5_OUT_A.DQ2: J1.91 (DQ30_A)
LPDDR5_OUT_A.DQ3: J1.87 (DQ28_A)
LPDDR5_OUT_A.DQ4: J1.76 (DQ25_A)
LPDDR5_OUT_A.DQ5: J1.73 (DQ24_A)
LPDDR5_OUT_A.DQ6: J1.77 (DQ26_A)
LPDDR5_OUT_A.DQ7: J1.80 (DQ27_A)
LPDDR5_OUT_A.DQ8: J1.31 (DQ8_A)
LPDDR5_OUT_A.DQ9: J1.35 (DQ10_A)
LPDDR5_OUT_A.DQ10: J1.34 (DQ09_A)
LPDDR5_OUT_A.DQ11: J1.38 (DQ11_A)
LPDDR5_OUT_A.DQ12: J1.49 (DQ14_A)
LPDDR5_OUT_A.DQ13: J1.50 (DQ15_A)
LPDDR5_OUT_A.DQ14: J1.46 (DQ13_A)
LPDDR5_OUT_A.DQ15: J1.45 (DQ12_A)
LPDDR5_OUT_A.RDQS0_N: J1.81 (DQS3_A_C)
LPDDR5_OUT_A.RDQS0_P: J1.83 (DQS3_A_t)
LPDDR5_OUT_A.RDQS1_N: J1.39 (DQS1_A_C)
LPDDR5_OUT_A.RDQS1_P: J1.41 (DQS1_A_t)
LPDDR5_OUT_B.DMI0: J1.229 (DM2_B_n)
LPDDR5_OUT_B.DMI1: J1.187 (DM0_B_n)
LPDDR5_OUT_B.DQ0: J1.240 (DQ23_B)
LPDDR5_OUT_B.DQ1: J1.236 (DQ21_B)
LPDDR5_OUT_B.DQ2: J1.237 (DQ22_B)
LPDDR5_OUT_B.DQ3: J1.233 (DQ20_B)
LPDDR5_OUT_B.DQ4: J1.222 (DQ17_B)
LPDDR5_OUT_B.DQ5: J1.221 (DQ16_B)
LPDDR5_OUT_B.DQ6: J1.225 (DQ18_B)
LPDDR5_OUT_B.DQ7: J1.226 (DQ19_B)
LPDDR5_OUT_B.DQ8: J1.179 (DQ0_B)
LPDDR5_OUT_B.DQ9: J1.183 (DQ2_B)
LPDDR5_OUT_B.DQ10: J1.180 (DQ1_B)
LPDDR5_OUT_B.DQ11: J1.184 (DQ3_B)
LPDDR5_OUT_B.DQ12: J1.195 (DQ6_B)
LPDDR5_OUT_B.DQ13: J1.198 (DQ7_B)
LPDDR5_OUT_B.DQ14: J1.194 (DQ5_B)
LPDDR5_OUT_B.DQ15: J1.191 (DQ4_B)
LPDDR5_OUT_B.RDQS0_N: J1.230 (DQS2_B_C)
LPDDR5_OUT_B.RDQS0_P: J1.232 (DQS2_B_t)
LPDDR5_OUT_B.RDQS1_N: J1.188 (DQS0_B_C)
LPDDR5_OUT_B.RDQS1_P: J1.190 (DQS0_B_t)
unnamed: J1.130 (TB_DETECT), R28.2, R99.1
PWRGD: J1.7 (PWR_GOOD)
PWR_EN: J1.8 (PWR_EN)
~RESET: J1.163 (RESET_n)

Notes on the sheet:
SODIMM Connector
