antmicro/lpddr5-testbed/translators.kicad_sch

## KiCad design translators.kicad_sch (2023-12-29)

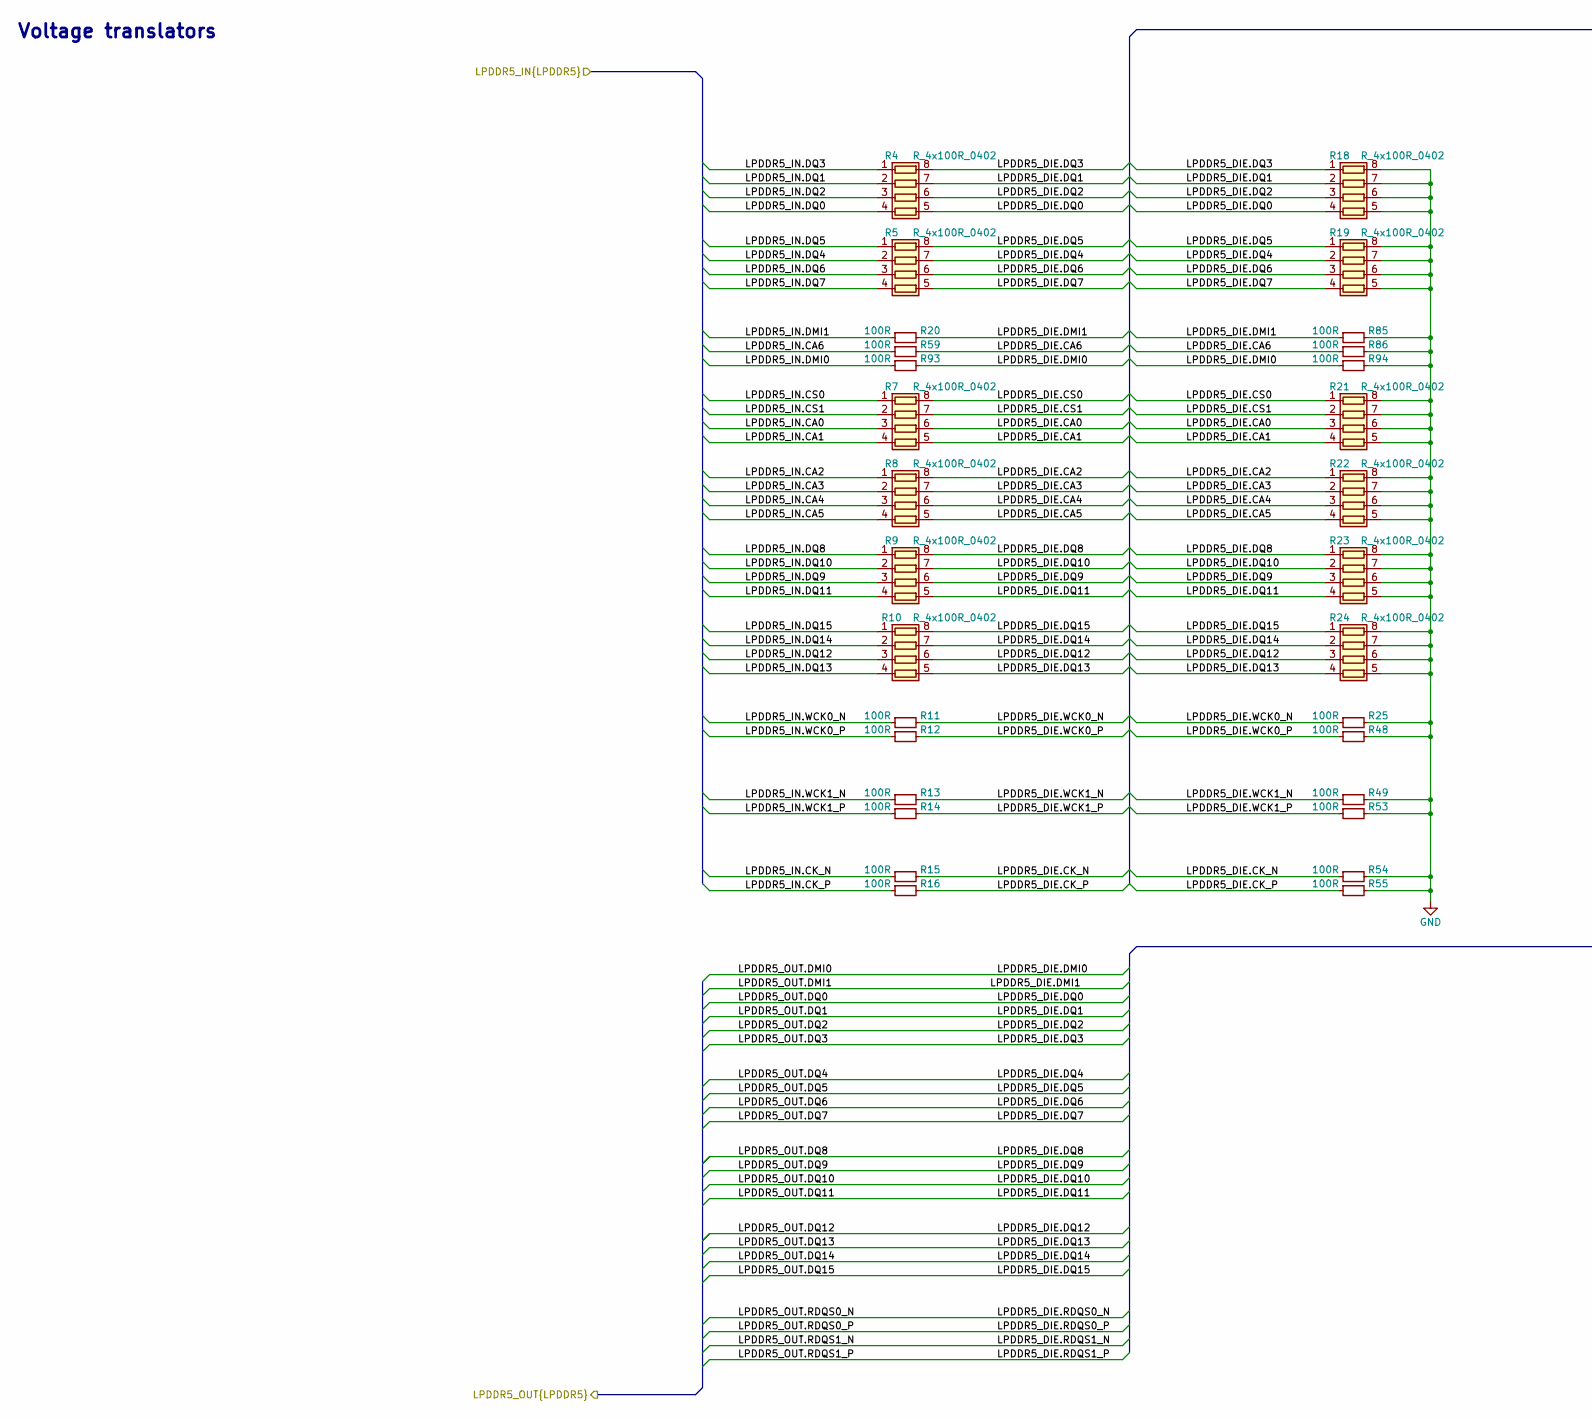
[picture p23: schematic translators.kicad_sch, part in row 1, column 1]

Parts:
R4, R5, R7, R8, R9, R10, R18, R19, R21, R22, R23, R24: R_4x100R_0402_array; R_Array_4x0402_Panasonic_EXB28V; MPN EXB-28V101JX
R11, R12, R13, R14, R15, R16, R20, R25, R48, R49, R53, R54, R55, R59, R85, R86, R93, R94: R_100R_0402; R_0402_1005Metric; Tolerance 1%; MPN CR0402-FX-1000GLF

Connections:
GND: R18.5 (R4.2), R18.6 (R3.2), R18.7 (R2.2), R18.8 (R1.2), R19.5 (R4.2), R19.6 (R3.2), R19.7 (R2.2), R19.8 (R1.2), R21.5 (R4.2), R21.6 (R3.2), R21.7 (R2.2), R21.8 (R1.2), R22.5 (R4.2), R22.6 (R3.2), R22.7 (R2.2), R22.8 (R1.2), R23.5 (R4.2), R23.6 (R3.2), R23.7 (R2.2), R23.8 (R1.2), R24.5 (R4.2), R24.6 (R3.2), R24.7 (R2.2), R24.8 (R1.2), R25.2, R48.2, R49.2, R53.2, R54.2, R55.2, R85.2, R86.2, R94.2
LPDDR5_DIE.CA0: R7.6 (R3.2), R21.3 (R3.1)
LPDDR5_DIE.CA1: R7.5 (R4.2), R21.4 (R4.1)
LPDDR5_DIE.CA2: R8.8 (R1.2), R22.1 (R1.1)
LPDDR5_DIE.CA3: R8.7 (R2.2), R22.2 (R2.1)
LPDDR5_DIE.CA4: R8.6 (R3.2), R22.3 (R3.1)
LPDDR5_DIE.CA5: R8.5 (R4.2), R22.4 (R4.1)
LPDDR5_DIE.CA6: R59.2, R86.1
LPDDR5_DIE.CK_N: R15.2, R54.1
LPDDR5_DIE.CK_P: R16.2, R55.1
LPDDR5_DIE.CS0: R7.8 (R1.2), R21.1 (R1.1)
LPDDR5_DIE.CS1: R7.7 (R2.2), R21.2 (R2.1)
LPDDR5_DIE.DMI0: R93.2, R94.1
LPDDR5_DIE.DMI1: R20.2, R85.1
LPDDR5_DIE.DQ0: R4.5 (R4.2), R18.4 (R4.1)
LPDDR5_DIE.DQ1: R4.7 (R2.2), R18.2 (R2.1)
LPDDR5_DIE.DQ2: R4.6 (R3.2), R18.3 (R3.1)
LPDDR5_DIE.DQ3: R4.8 (R1.2), R18.1 (R1.1)
LPDDR5_DIE.DQ4: R5.7 (R2.2), R19.2 (R2.1)
LPDDR5_DIE.DQ5: R5.8 (R1.2), R19.1 (R1.1)
LPDDR5_DIE.DQ6: R5.6 (R3.2), R19.3 (R3.1)
LPDDR5_DIE.DQ7: R5.5 (R4.2), R19.4 (R4.1)
LPDDR5_DIE.DQ8: R9.8 (R1.2), R23.1 (R1.1)
LPDDR5_DIE.DQ9: R9.6 (R3.2), R23.3 (R3.1)
LPDDR5_DIE.DQ10: R9.7 (R2.2), R23.2 (R2.1)
LPDDR5_DIE.DQ11: R9.5 (R4.2), R23.4 (R4.1)
LPDDR5_DIE.DQ12: R10.6 (R3.2), R24.3 (R3.1)
LPDDR5_DIE.DQ13: R10.5 (R4.2), R24.4 (R4.1)
LPDDR5_DIE.DQ14: R10.7 (R2.2), R24.2 (R2.1)
LPDDR5_DIE.DQ15: R10.8 (R1.2), R24.1 (R1.1)
LPDDR5_DIE.WCK0_N: R11.2, R25.1
LPDDR5_DIE.WCK0_P: R12.2, R48.1
LPDDR5_DIE.WCK1_N: R13.2, R49.1
LPDDR5_DIE.WCK1_P: R14.2, R53.1
LPDDR5_IN.CA0: R7.3 (R3.1)
LPDDR5_IN.CA1: R7.4 (R4.1)
LPDDR5_IN.CA2: R8.1 (R1.1)
LPDDR5_IN.CA3: R8.2 (R2.1)
LPDDR5_IN.CA4: R8.3 (R3.1)
LPDDR5_IN.CA5: R8.4 (R4.1)
LPDDR5_IN.CA6: R59.1
LPDDR5_IN.CK_N: R15.1
LPDDR5_IN.CK_P: R16.1
LPDDR5_IN.CS0: R7.1 (R1.1)
LPDDR5_IN.CS1: R7.2 (R2.1)
LPDDR5_IN.DMI0: R93.1
LPDDR5_IN.DMI1: R20.1
LPDDR5_IN.DQ0: R4.4 (R4.1)
LPDDR5_IN.DQ1: R4.2 (R2.1)
LPDDR5_IN.DQ2: R4.3 (R3.1)
LPDDR5_IN.DQ3: R4.1 (R1.1)
LPDDR5_IN.DQ4: R5.2 (R2.1)
LPDDR5_IN.DQ5: R5.1 (R1.1)
LPDDR5_IN.DQ6: R5.3 (R3.1)
LPDDR5_IN.DQ7: R5.4 (R4.1)
LPDDR5_IN.DQ8: R9.1 (R1.1)
LPDDR5_IN.DQ9: R9.3 (R3.1)
LPDDR5_IN.DQ10: R9.2 (R2.1)
LPDDR5_IN.DQ11: R9.4 (R4.1)
LPDDR5_IN.DQ12: R10.3 (R3.1)
LPDDR5_IN.DQ13: R10.4 (R4.1)
LPDDR5_IN.DQ14: R10.2 (R2.1)
LPDDR5_IN.DQ15: R10.1 (R1.1)
LPDDR5_IN.WCK0_N: R11.1
LPDDR5_IN.WCK0_P: R12.1
LPDDR5_IN.WCK1_N: R13.1
LPDDR5_IN.WCK1_P: R14.1

Notes on the sheet:
Voltage translators
